Xartos/crkbd/pcbs/common/left.kicad_sch

## KiCad design pcbs/common/left.kicad_sch (2024-04-23)

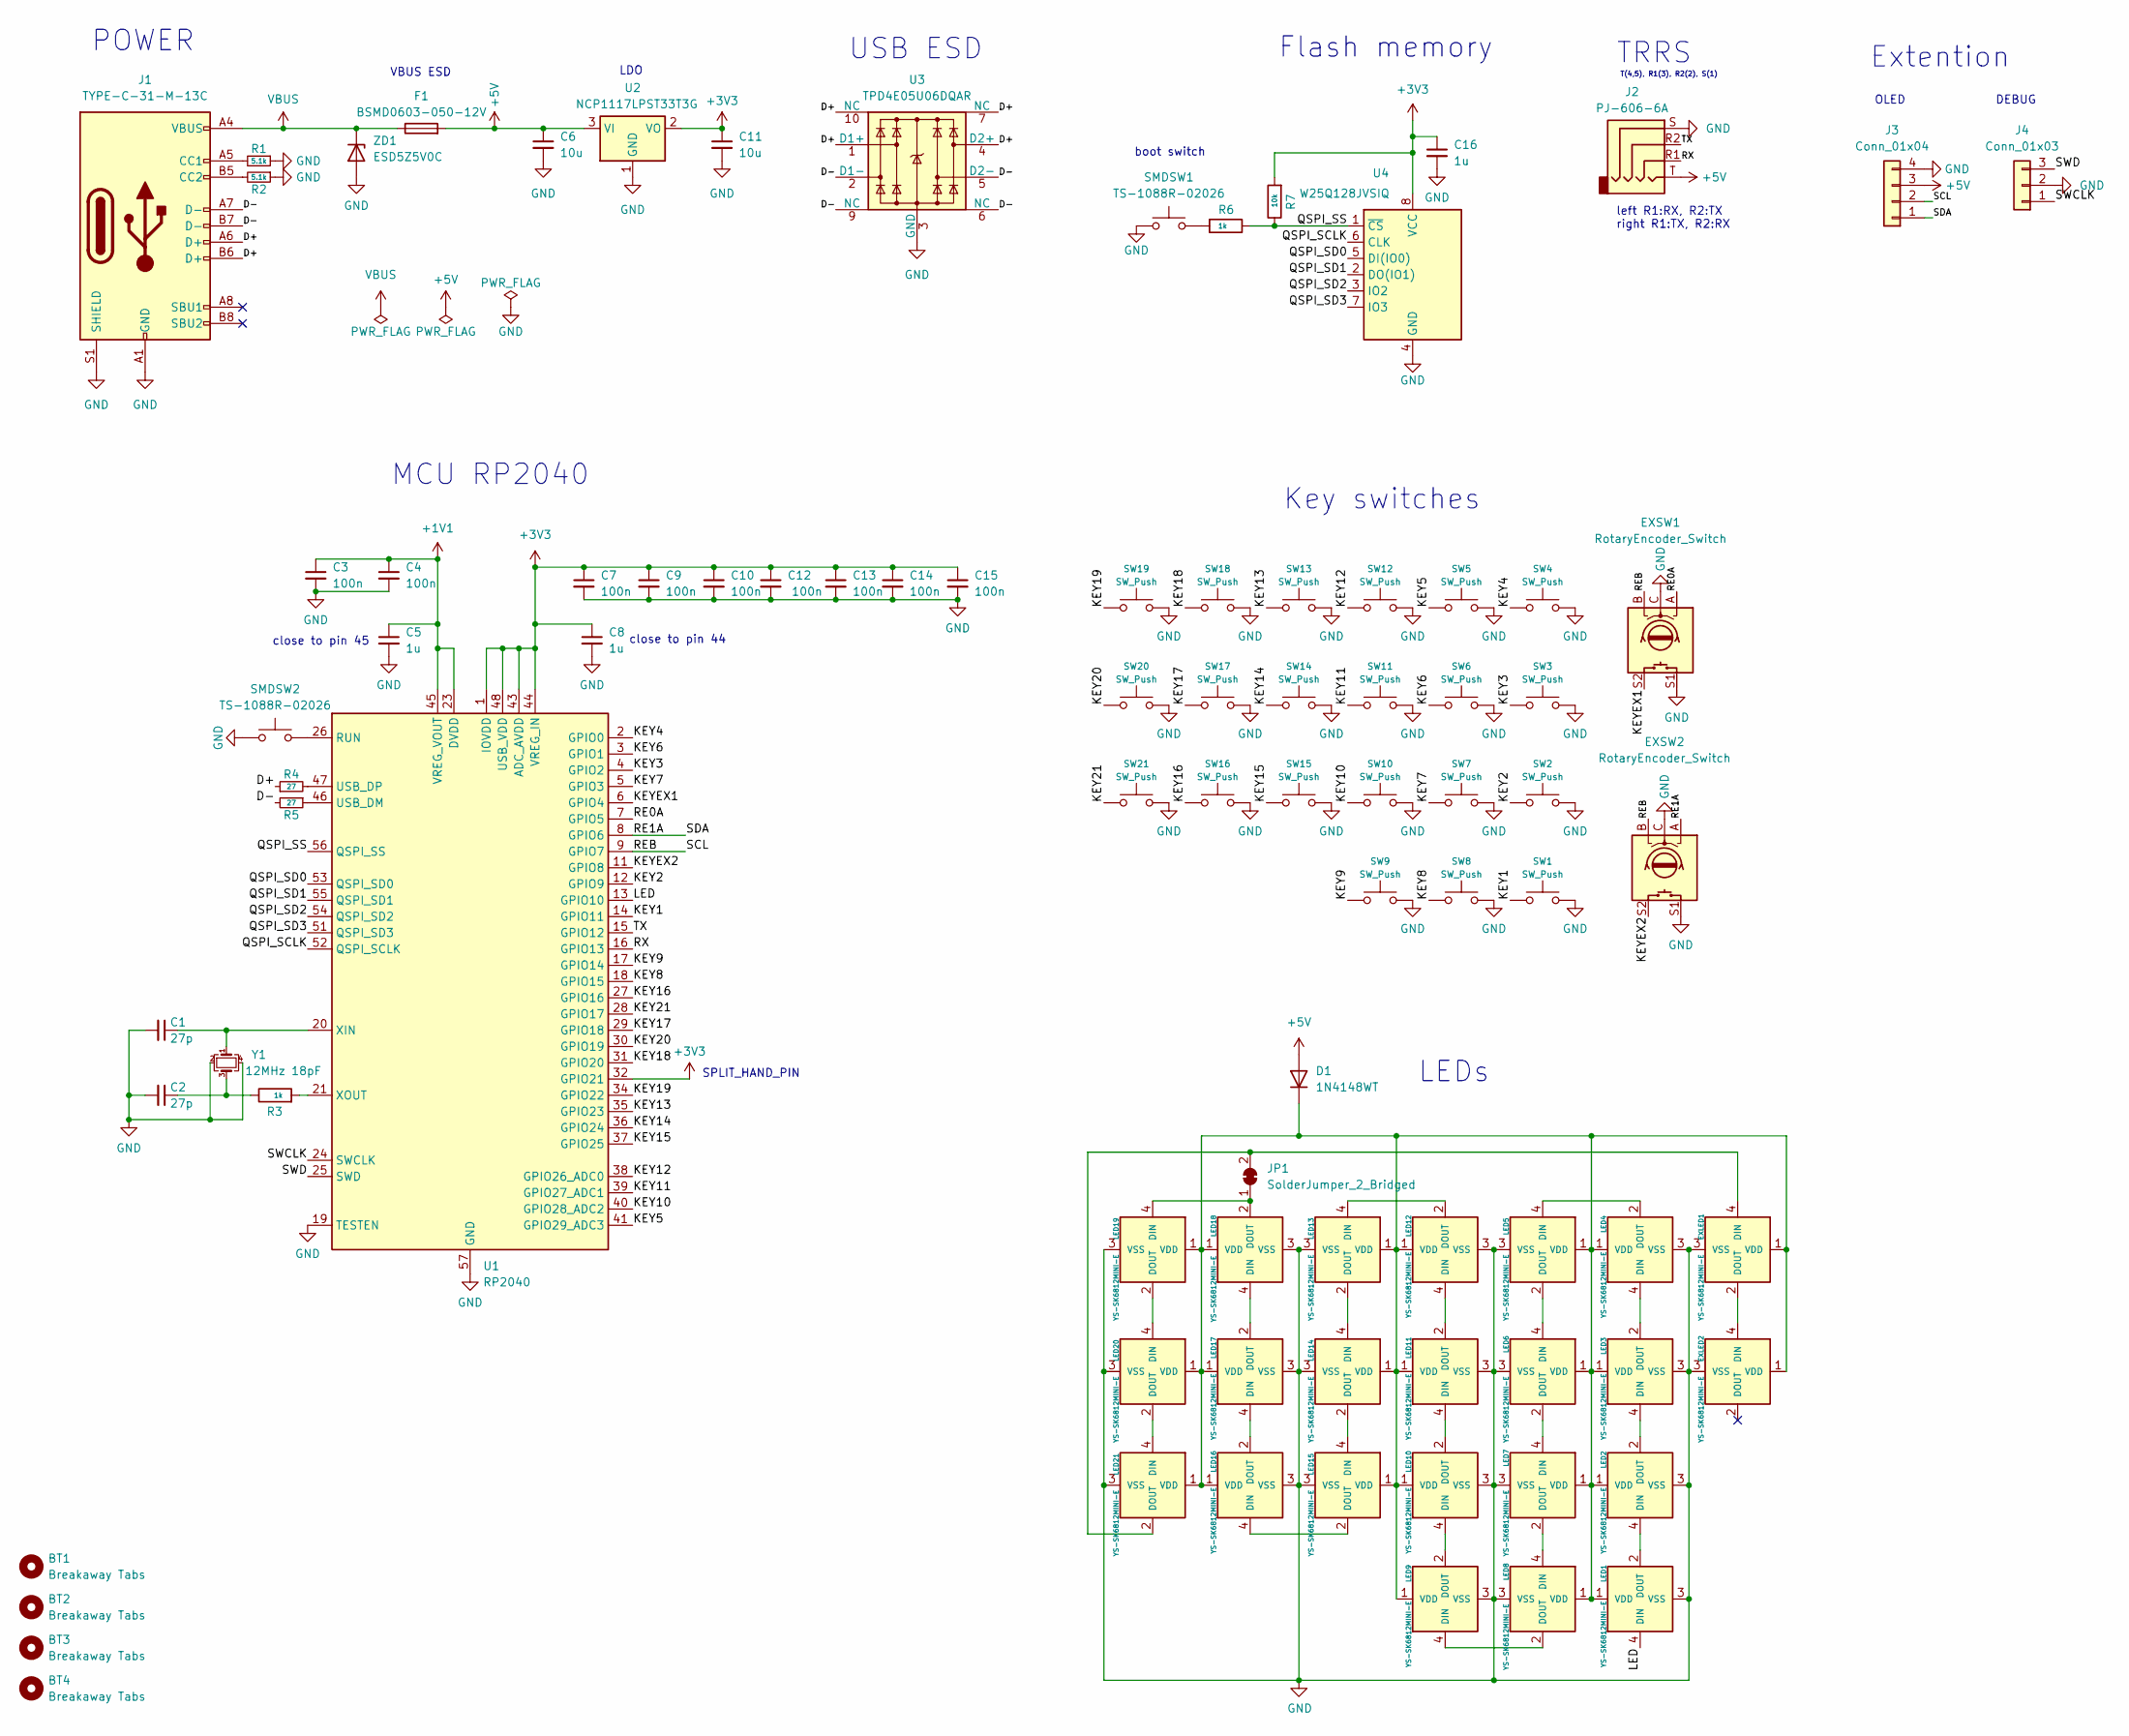
[picture p3: schematic left.kicad_sch]

Parts:
BT1, BT2, BT3, BT4: Breakaway Tabs; Breakaway_Tabs
C1, C2: 27p; C_0402_1005Metric
C3, C4, C7, C9, C10, C12, C13, C14, C15: 100n; C_0402_1005Metric
C5, C8, C16: 1u; C_0402_1005Metric
C6, C11: 10u; C_0402_1005Metric
D1: 1N4148WT; D_SOD-523; JLCPCB Part # C232841
EXLED1, EXLED2: YS-SK6812MINI-E; JLCPCB Part # C5149201
EXSW1, EXSW2: RotaryEncoder_Switch; keyswitch_choc12_hotswap_1u_rotary_encoder_ec12; JLCPCB Part # C5333465
F1: BSMD0603-050-12V; Fuse_0603_1608Metric; JLCPCB Part # C2844464
J1: TYPE-C-31-M-13C; JLCPCB Part # C2848620
J2: PJ-606-6A; JLCPCB Part # C145806
J3: Conn_01x04; OLED
J4: Conn_01x03; PinHeader_1x03_P2.54mm_Vertical
JP1: SolderJumper_2_Bridged; SolderJumper-2_P1.3mm_Open_RoundedPad1.0x1.5mm
LED1, LED2, LED3, LED4, LED5, LED6, LED7, LED8, LED9, LED10, LED11, LED12, LED13, LED14, LED15, LED16, LED17, LED18, LED19, LED20, LED21: YS-SK6812MINI-E; JLCPCB Part # C5149201
R1, R2: 5.1k; R_0402_1005Metric
R3, R6: 1k; R_0402_1005Metric
R4, R5: 27; R_0402_1005Metric
R7: 10k; R_0402_1005Metric
SMDSW1, SMDSW2: TS-1088R-02026; JLCPCB Part # C455280
SW1: SW_Push; keyswitch_choc12_hotswap_1.5u; JLCPCB Part # C5333465
SW2, SW3, SW4, SW5, SW6, SW7, SW8, SW9, SW10, SW11, SW12, SW13, SW14, SW15, SW16, SW17, SW18, SW19, SW20, SW21: SW_Push; keyswitch_choc12_hotswap_1u; JLCPCB Part # C5333465
U1: RP2040; QFN-56-1EP_7x7mm_P0.4mm_EP3.2x3.2mm; JLCPCB Part # C2040
U2: NCP1117LPST33T3G; SOT-223-3_TabPin2; JLCPCB Part # C146799
U3: TPD4E05U06DQAR; USON-10_2.5x1.0mm_P0.5mm; JLCPCB Part # C138714
U4: W25Q128JVSIQ; SOIC-8_5.23x5.23mm_P1.27mm; JLCPCB Part # C113767
Y1: 12MHz 18pF; Crystal_SMD_3225-4Pin_3.2x2.5mm; MFR.Part # Q22FA23V0041800; JLCPCB Part # C91749
ZD1: ESD5Z5V0C; D_SOD-523; JLCPCB Part # C2901325

Connections:
+1V1: C3.1, C4.1, C5.1, U1.23 (DVDD), U1.45 (VREG_VOUT), U1.50 (DVDD)
+3V3: C7.1, C8.1, C9.1, C10.1, C11.1, C12.1, C13.1, C14.1, C15.1, C16.1, R7.2, U1.1 (IOVDD), U1.10 (IOVDD), U1.22 (IOVDD), U1.32 (GPIO21), U1.33 (IOVDD), U1.42 (IOVDD), U1.43 (ADC_AVDD), U1.44 (VREG_IN), U1.48 (USB_VDD), U1.49 (IOVDD), U2.2 (VO), U4.8 (VCC)
+5V: C6.1, D1.2 (A), F1.2, J2.T, J3.3, U2.3 (VI)
D+: J1.A6 (D+), J1.B6 (D+), R4.1, U3.1 (D1+), U3.4 (D2+), U3.7 (NC), U3.10 (NC)
D-: J1.A7 (D-), J1.B7 (D-), R5.2, U3.2 (D1-), U3.5 (D2-), U3.6 (NC), U3.9 (NC)
GND: C1.2, C2.2, C3.2, C4.2, C5.2, C6.2, C7.2, C8.2, C9.2, C10.2, C11.2, C12.2, C13.2, C14.2, C15.2, C16.2, EXLED1.3 (VSS), EXLED2.3 (VSS), EXSW1.C, EXSW1.S1, EXSW2.C, EXSW2.S1, J1.A1 (GND), J1.A12 (GND), J1.B1 (GND), J1.B12 (GND), J1.S1 (SHIELD), J2.S, J3.4, J4.2, LED1.3 (VSS), LED2.3 (VSS), LED3.3 (VSS), LED4.3 (VSS), LED5.3 (VSS), LED6.3 (VSS), LED7.3 (VSS), LED8.3 (VSS), LED9.3 (VSS), LED10.3 (VSS), LED11.3 (VSS), LED12.3 (VSS), LED13.3 (VSS), LED14.3 (VSS), LED15.3 (VSS), LED16.3 (VSS), LED17.3 (VSS), LED18.3 (VSS), LED19.3 (VSS), LED20.3 (VSS), LED21.3 (VSS), R1.1, R2.1, SMDSW1.1, SMDSW2.1, SW1.2, SW2.2, SW3.2, SW4.2, SW5.2, SW6.2, SW7.2, SW8.2, SW9.2, SW10.2, SW11.2, SW12.2, SW13.2, SW14.2, SW15.2, SW16.2, SW17.2, SW18.2, SW19.2, SW20.2, SW21.2, U1.19 (TESTEN), U1.57 (GND), U2.1 (GND), U3.3 (GND), U3.8 (GND), U4.4 (GND), Y1.2, Y1.4, ZD1.2 (A)
KEY1: SW1.1, U1.14 (GPIO11)
KEY2: SW2.1, U1.12 (GPIO9)
KEY3: SW3.1, U1.4 (GPIO2)
KEY4: SW4.1, U1.2 (GPIO0)
KEY5: SW5.1, U1.41 (GPIO29_ADC3)
KEY6: SW6.1, U1.3 (GPIO1)
KEY7: SW7.1, U1.5 (GPIO3)
KEY8: SW8.1, U1.18 (GPIO15)
KEY9: SW9.1, U1.17 (GPIO14)
KEY10: SW10.1, U1.40 (GPIO28_ADC2)
KEY11: SW11.1, U1.39 (GPIO27_ADC1)
KEY12: SW12.1, U1.38 (GPIO26_ADC0)
KEY13: SW13.1, U1.35 (GPIO23)
KEY14: SW14.1, U1.36 (GPIO24)
KEY15: SW15.1, U1.37 (GPIO25)
KEY16: SW16.1, U1.27 (GPIO16)
KEY17: SW17.1, U1.29 (GPIO18)
KEY18: SW18.1, U1.31 (GPIO20)
KEY19: SW19.1, U1.34 (GPIO22)
KEY20: SW20.1, U1.30 (GPIO19)
KEY21: SW21.1, U1.28 (GPIO17)
KEYEX1: EXSW1.S2, U1.6 (GPIO4)
KEYEX2: EXSW2.S2, U1.11 (GPIO8)
LED: LED1.4 (DIN), U1.13 (GPIO10)
unnamed: C1.1, U1.20 (XIN), Y1.1
unnamed: C2.1, R3.1, Y1.3
unnamed: D1.1 (K), EXLED1.1 (VDD), EXLED2.1 (VDD), LED1.1 (VDD), LED2.1 (VDD), LED3.1 (VDD), LED4.1 (VDD), LED5.1 (VDD), LED6.1 (VDD), LED7.1 (VDD), LED8.1 (VDD), LED9.1 (VDD), LED10.1 (VDD), LED11.1 (VDD), LED12.1 (VDD), LED13.1 (VDD), LED14.1 (VDD), LED15.1 (VDD), LED16.1 (VDD), LED17.1 (VDD), LED18.1 (VDD), LED19.1 (VDD), LED20.1 (VDD), LED21.1 (VDD)
unnamed: EXLED1.2 (DOUT), EXLED2.4 (DIN)
unnamed: EXLED1.4 (DIN), JP1.2 (B), LED21.2 (DOUT)
unnamed: J1.A5 (CC1), R1.2
unnamed: J1.B5 (CC2), R2.2
unnamed: JP1.1 (A), LED18.2 (DOUT), LED19.4 (DIN)
unnamed: LED1.2 (DOUT), LED2.4 (DIN)
unnamed: LED2.2 (DOUT), LED3.4 (DIN)
unnamed: LED3.2 (DOUT), LED4.4 (DIN)
unnamed: LED4.2 (DOUT), LED5.4 (DIN)
unnamed: LED5.2 (DOUT), LED6.4 (DIN)
unnamed: LED6.2 (DOUT), LED7.4 (DIN)
unnamed: LED7.2 (DOUT), LED8.4 (DIN)
unnamed: LED8.2 (DOUT), LED9.4 (DIN)
unnamed: LED10.2 (DOUT), LED11.4 (DIN)
unnamed: LED9.2 (DOUT), LED10.4 (DIN)
unnamed: LED11.2 (DOUT), LED12.4 (DIN)
unnamed: LED12.2 (DOUT), LED13.4 (DIN)
unnamed: LED13.2 (DOUT), LED14.4 (DIN)
unnamed: LED14.2 (DOUT), LED15.4 (DIN)
unnamed: LED15.2 (DOUT), LED16.4 (DIN)
unnamed: LED16.2 (DOUT), LED17.4 (DIN)
unnamed: LED17.2 (DOUT), LED18.4 (DIN)
unnamed: LED19.2 (DOUT), LED20.4 (DIN)
unnamed: LED20.2 (DOUT), LED21.4 (DIN)
unnamed: R3.2, U1.21 (XOUT)
unnamed: R4.2, U1.47 (USB_DP)
unnamed: R5.1, U1.46 (USB_DM)
unnamed: R6.2, SMDSW1.2
unnamed: SMDSW2.2, U1.26 (RUN)
QSPI_SCLK: U1.52 (QSPI_SCLK), U4.6 (CLK)
QSPI_SD0: U1.53 (QSPI_SD0), U4.5 (DI(IO0))
QSPI_SD1: U1.55 (QSPI_SD1), U4.2 (DO(IO1))
QSPI_SD2: U1.54 (QSPI_SD2), U4.3 (IO2)
QSPI_SD3: U1.51 (QSPI_SD3), U4.7 (IO3)
QSPI_SS: R6.1, R7.1, U1.56 (QSPI_SS), U4.1 (~CS)
RE0A: EXSW1.A, U1.7 (GPIO5)
RE1A: EXSW2.A, J3.1, U1.8 (GPIO6)
REB: EXSW1.B, EXSW2.B, J3.2, U1.9 (GPIO7)
RX: J2.R1, U1.16 (GPIO13)
SWCLK: J4.1, U1.24 (SWCLK)
SWD: J4.3, U1.25 (SWD)
TX: J2.R2, U1.15 (GPIO12)
VBUS: F1.1, J1.A4 (VBUS), J1.A9 (VBUS), J1.B4 (VBUS), J1.B9 (VBUS), ZD1.1 (K)

Notes on the sheet:
MCU RP2040
Key switches
OLED
close to pin 45
DEBUG
USB ESD
LDO
Flash memory
POWER
LEDs
left R1:RX, R2:TX right R1:TX, R2:RX
Extention
TRRS
T(4,5), R1(3), R2(2), S(1)
VBUS ESD
SPLIT_HAND_PIN
boot switch
close to pin 44
